ftkalcevic/EInkRainGauge/RainGaugeDigital/Debug.h

/*****************************************************************************
* | File      	:	Debug.h
* | Author      :   Waveshare team
* | Function    :	debug with printf
* | Info        :
*   Image scanning
*      Please use progressive scanning to generate images or fonts
*----------------
* |	This version:   V1.0
* | Date        :   2018-01-11
* | Info        :   Basic version
*
******************************************************************************/
#ifndef __DEBUG_H
#define __DEBUG_H

#ifdef DEBUG
	#define Debug(__info,...) printf(__info,##__VA_ARGS__)
#else
	#define Debug(__info,...)  
#endif

#endif
